r-hmn/micronova_stove_esphome/stove-ram-reader/micronova_stove.h

#include <Arduino.h>

// Original from: https://github.com/eni23/micronova-controller

/* =================================
 * Changelog
 * =================================
 * 2026-05-01  Changed timing to fit speedup for ARTEL IDRO.
 *             (Used "USB logic analyzer" to see dead-times in communication)
 * 2026-05-03  Added ARTEL addresses
 * =================================*/

#ifndef _MICRONOVA_STOVE_H
  #define _MICRONOVA_STOVE_H

#if defined(ESP8266) || defined(USE_SWSERIAL)
  #include <SoftwareSerial.h>
  extern SoftwareSerial StoveSerial;
  #define SERIAL_MODE SWSERIAL_8N2 
#endif

#if defined(ESP32) || defined(USE_HWSERIAL)
  #include <HardwareSerial.h>
  extern HardwareSerial StoveSerial;
  #define SERIAL_MODE SERIAL_8N2 
#endif


#define STOVE_OFFSET_RAM_READ     0x00
#define STOVE_OFFSET_EEPROM_READ  0x20
#define STOVE_OFFSET_RAM_WRITE    0x80
#define STOVE_OFFSET_EEPROM_WRITE 0xA0

// addresses
#define STOVE_ADDR_AMBIENT_TEMP   0x01 /*   1 */
#define STOVE_ADDR_STATE          0x21 /*  33 */
#define STOVE_ADDR_FUMES_TEMP     0x3E /*  62 */
#define STOVE_ADDR_FUMES_SPEED    0x37 /*  55 */
#define STOVE_ADDR_POWER_RAM      0x34 /*  52 */
#define STOVE_ADDR_POWER_EEPROM   0x7F /* 127 */
#define STOVE_ADDR_IRCOMMAND      0x58 /*  88 */
#define STOVE_ADDR_THERMOSTAT     0x7D /* 125 */
// Extra: Stove "ARTEL - IDRO 15 GPAR" addressess
#define STOVE_ADDR_ARTEL_FUMES_TEMP     88 /* 0x58 */
#define STOVE_ADDR_ARTEL_WATER_TEMP     3
#define STOVE_ADDR_ARTEL_WATER_PRESS    60 /* 0x3C */

// STATE
#define STOVE_STATE_TURN_ON       0x01
#define STOVE_STATE_TURN_OFF      0x06
#define STOVE_STATE_FORCE_OFF     0x00


// IRCOMMANDS
#define STOVE_IR_POWERUP          0x50
#define STOVE_IR_POWERDOWN        0x54
#define STOVE_IR_TEMPUP           0x52
#define STOVE_IR_TEMPDOWN         0x58
#define STOVE_IR_POWER            0x5A

/*0 - OFF, 
  1 - Starting, 
  2 - Pellet loading, 
  3 - Ignition, 
  4 - Work, 
  5 - Brazier cleaning, 
  6 - Final cleaning, 
  7 - Standby, 
  8 - Pellet missing alarm, 
  9 - Ignition failure alarm,
  10 - Alarms (to be investigated)
*/

class MicronovaStove {

  private:

    int pin_rx;
    int pin_tx;
    int pin_rx_enable;

  public:

    bool dbg_out = true;
    char stove_rx_data[2];
    uint8_t last_read_value;
    uint8_t last_read_param;
    uint8_t last_read_checksum;

    MicronovaStove( int rx, int tx, int rx_enable );

    void init();

    /* read functions */
    void enable_rx();
    void disable_rx();
    void flushInput();
    void read(uint8_t location, uint8_t addr);
    uint8_t read_ram( uint8_t addr );
    uint8_t read_eeprom( uint8_t addr );

    /* write functions */
    void write( uint8_t location, uint8_t command, uint8_t data );
    void write_ram( uint8_t command, uint8_t data );
    void write_eeprom( uint8_t command, uint8_t data );
    void simulate_infrared(uint8_t data, uint8_t repetitions );
    byte calculate_checksum( uint8_t dest, uint8_t addr, uint8_t val );
    void read_answer();

    /* misc abstraction functions */
    uint8_t get_state();
    void on();
    void off();
    float get_ambient_temp();
    uint8_t get_fumes_temp();
    uint8_t get_power();
    uint16_t get_fumes_fan_speed();
    void set_power(uint8_t power_level);

    void set_thermostat(uint8_t temperature);



};


#endif
